ashudhekne/MoViz/HardwareFiles/JLCPCB_BOM_CPL/Produce_DanZhi.SMT_Snapshot.Top.5348630A_Y8.SMT02308171359228.png

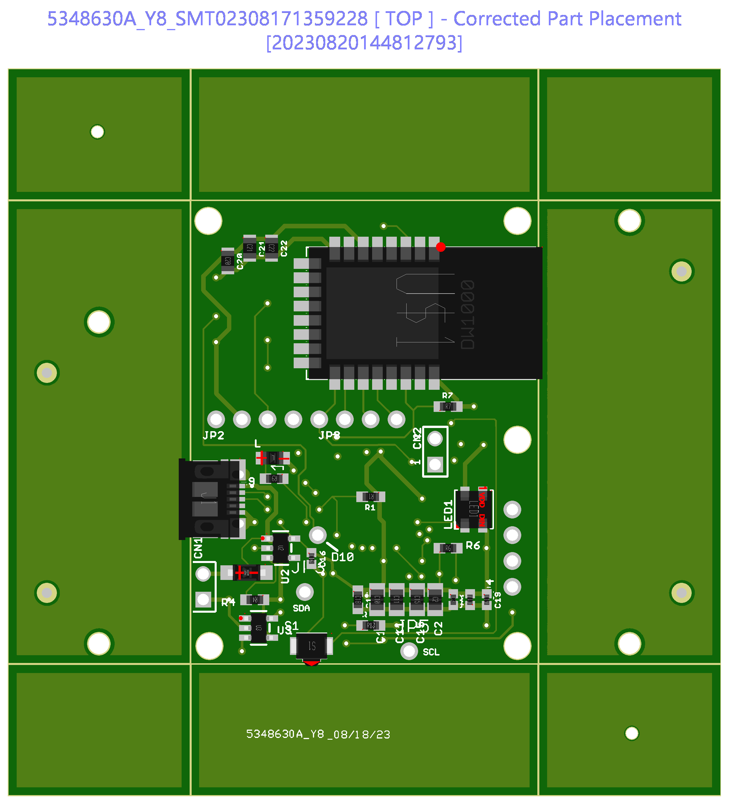
HardwareFiles/JLCPCB_BOM_CPL/Produce_DanZhi.SMT_Snapshot.Top.5348630A_Y8.SMT02308171359228.png
